funi-fi/ciivii/Hardware/.svg2shenzhen-cache/images/F.Cu_g29458.png

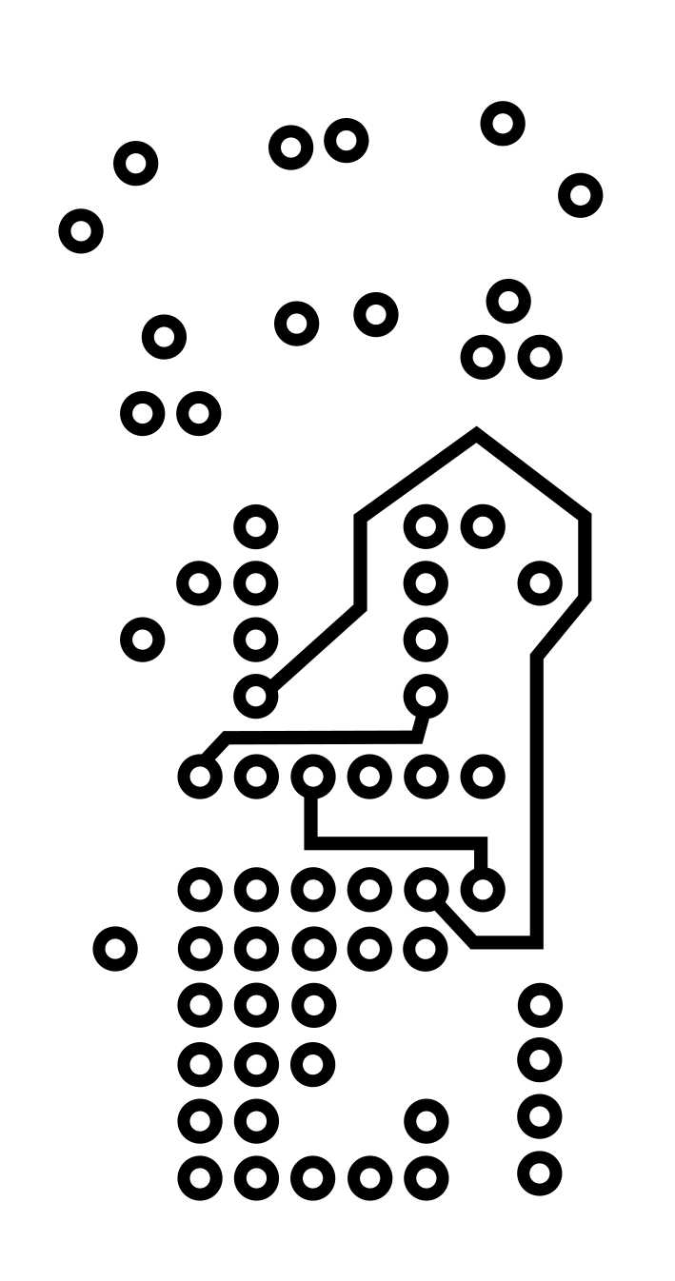
Hardware/.svg2shenzhen-cache/images/F.Cu_g29458.png
