funi-fi/ciivii/Pics/CiiVii_Solder_Guide/20190522_215049.jpg

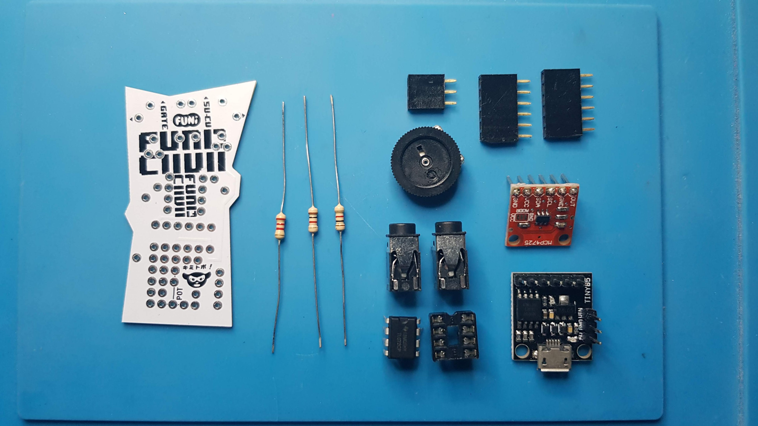
Pics/CiiVii_Solder_Guide/20190522_215049.jpg
