funi-fi/ciivii/Pics/CiiVii_Solder_Guide/20190522_220350.jpg

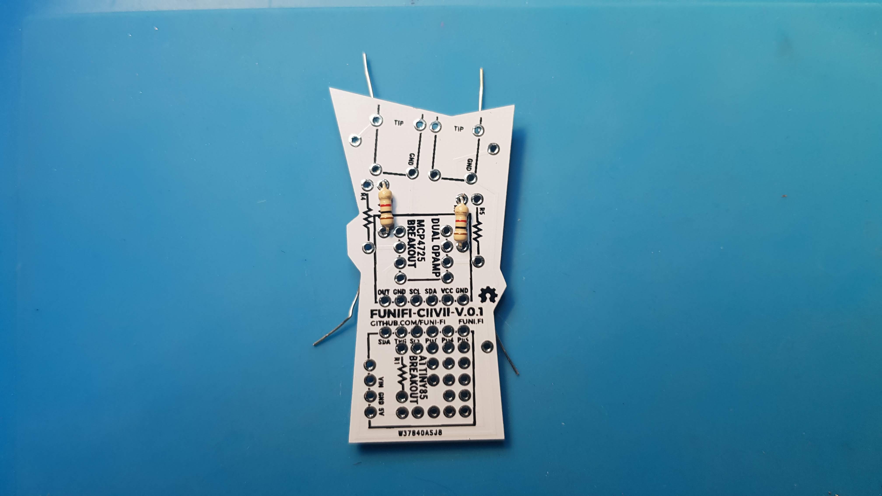
Pics/CiiVii_Solder_Guide/20190522_220350.jpg
