funi-fi/ciivii/Pics/CiiVii_Solder_Guide/20190522_220622.jpg

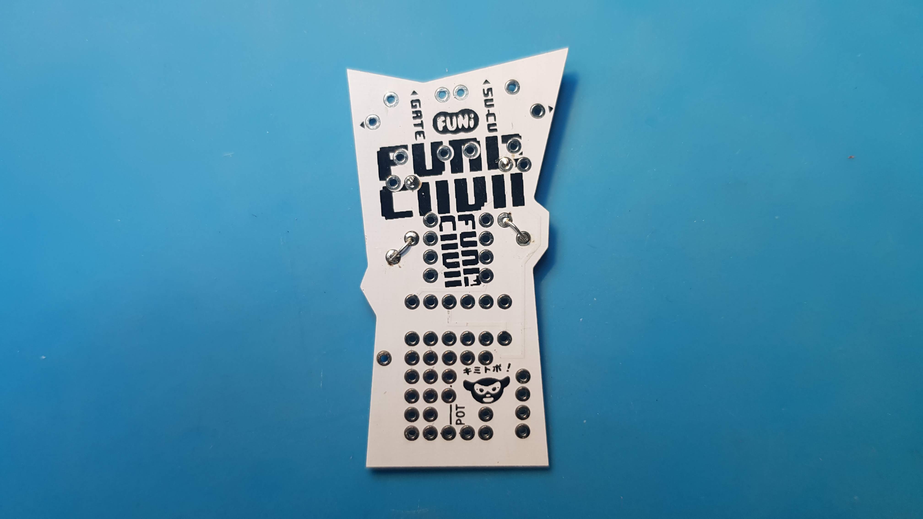
Pics/CiiVii_Solder_Guide/20190522_220622.jpg
