funi-fi/ciivii/Pics/CiiVii_Solder_Guide/20190522_221224.jpg

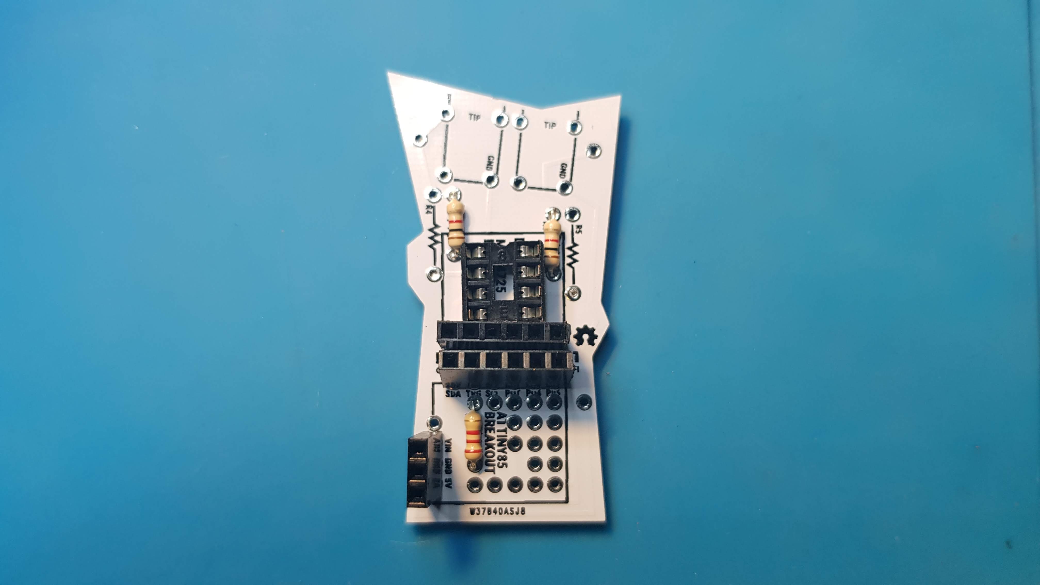
Pics/CiiVii_Solder_Guide/20190522_221224.jpg
