funi-fi/ciivii/Pics/CiiVii_Solder_Guide/20190522_221803.jpg

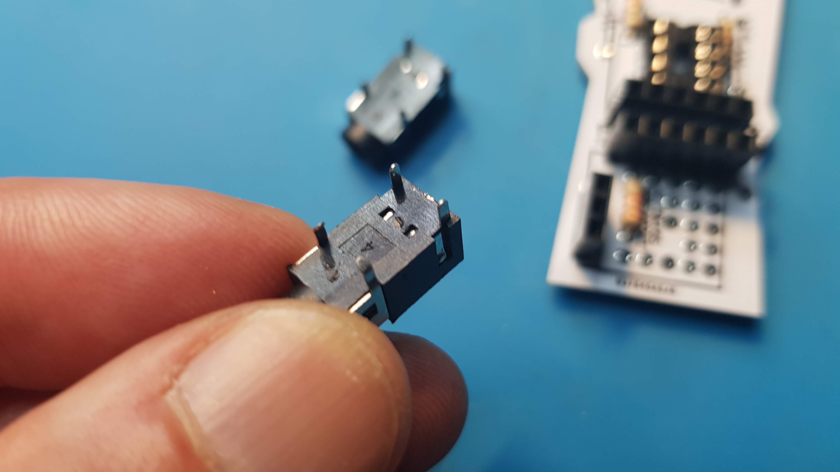
Pics/CiiVii_Solder_Guide/20190522_221803.jpg
