funi-fi/ciivii/Pics/CiiVii_Solder_Guide/20190522_222646.jpg

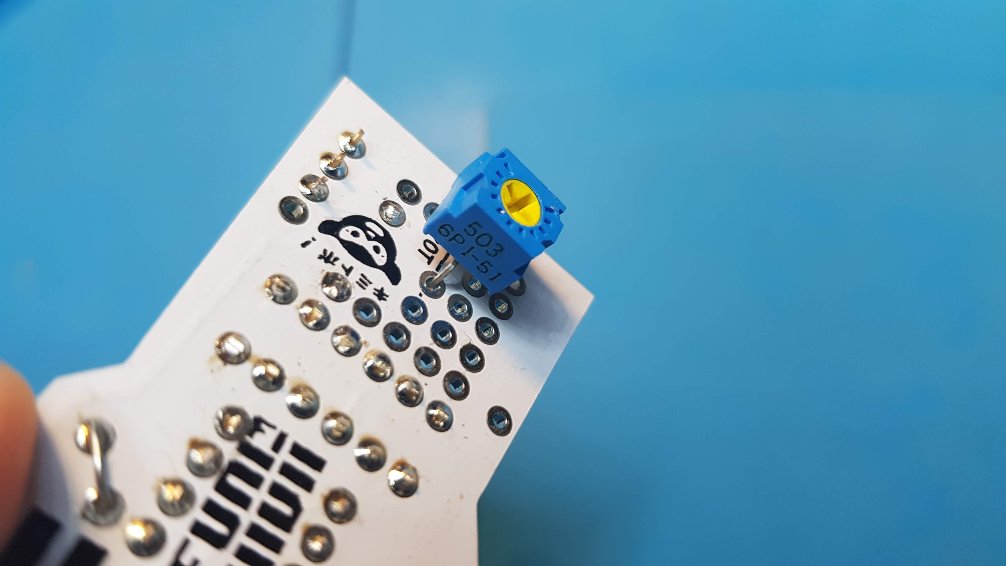
Pics/CiiVii_Solder_Guide/20190522_222646.jpg
