funi-fi/ciivii/Pics/CiiVii_Solder_Guide/20190522_223048.jpg

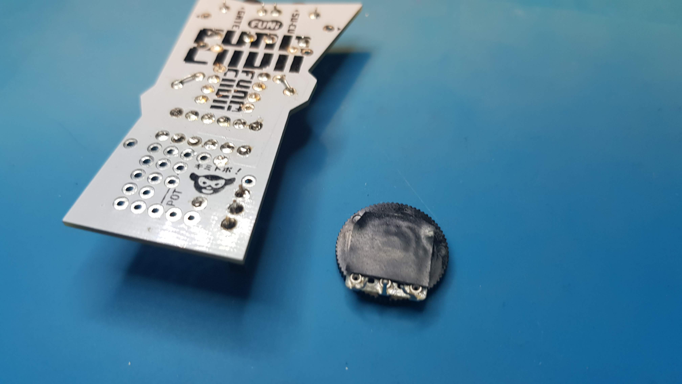
Pics/CiiVii_Solder_Guide/20190522_223048.jpg
