funi-fi/ciivii/Pics/CiiVii_Solder_Guide/20190522_223703.jpg

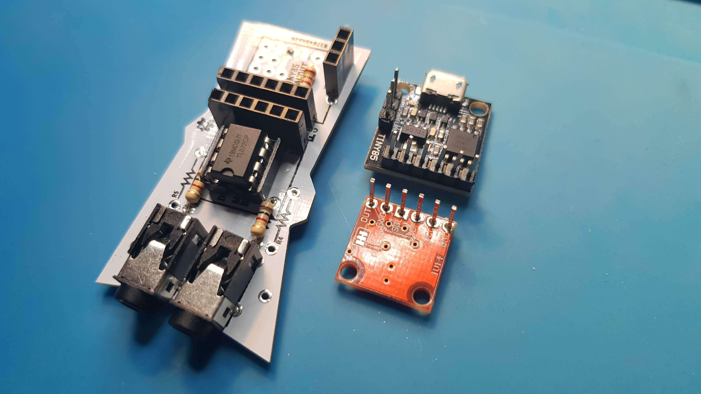
Pics/CiiVii_Solder_Guide/20190522_223703.jpg
