funi-fi/ciivii/Pics/CiiVii_Solder_Guide/20190522_223759.jpg

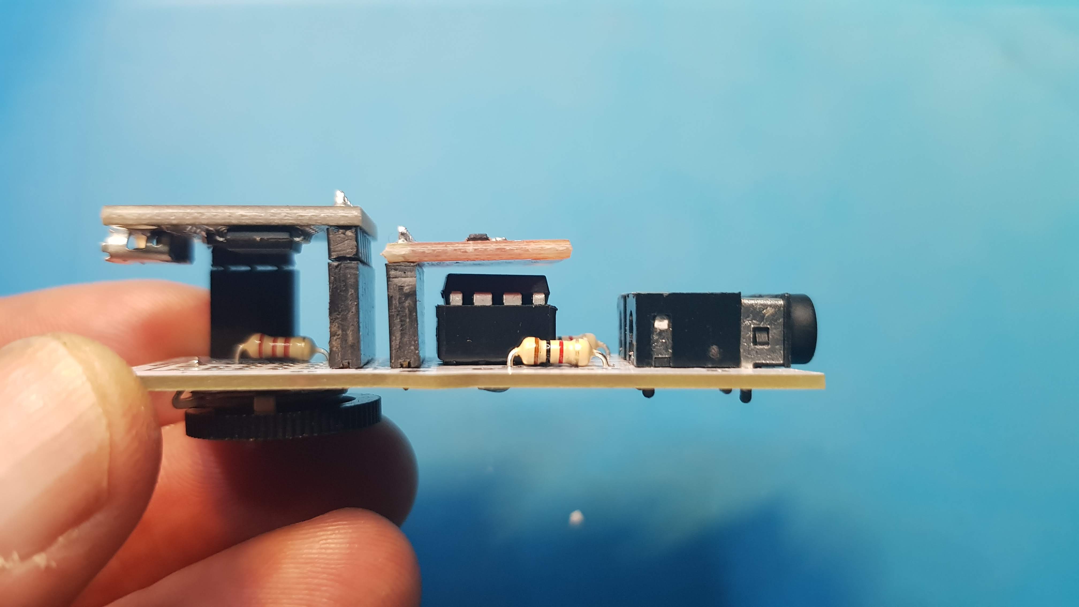
Pics/CiiVii_Solder_Guide/20190522_223759.jpg
