funi-fi/ciivii/Pics/CiiVii_Solder_Guide/20190522_224205.jpg

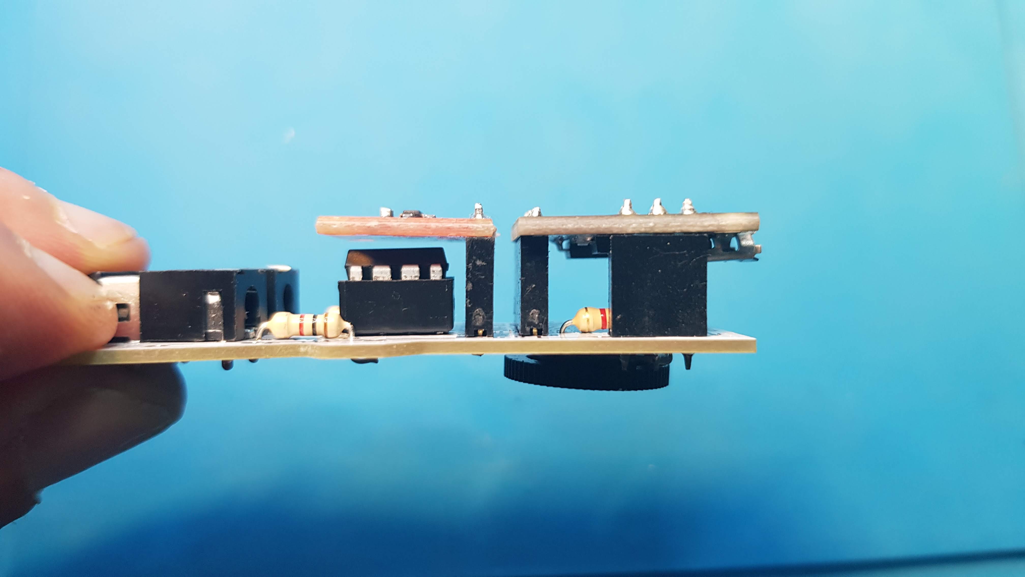
Pics/CiiVii_Solder_Guide/20190522_224205.jpg
