funi-fi/ciivii/Pics/CiiVii_Solder_Guide/20190522_224304.jpg

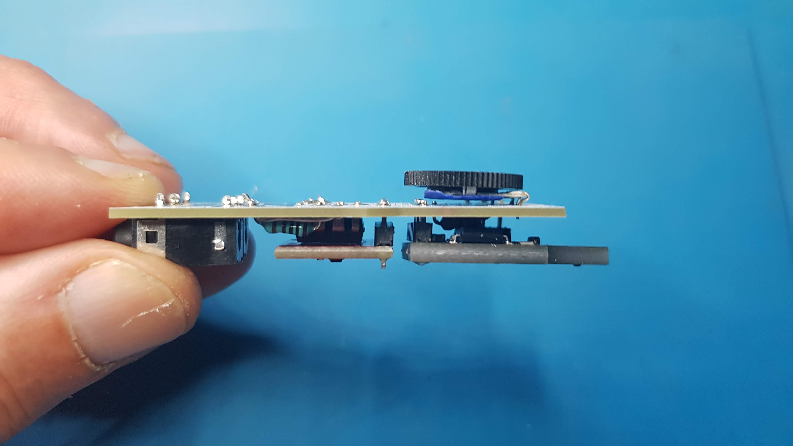
Pics/CiiVii_Solder_Guide/20190522_224304.jpg
